Sadrita404/Blinky/Images/1.png

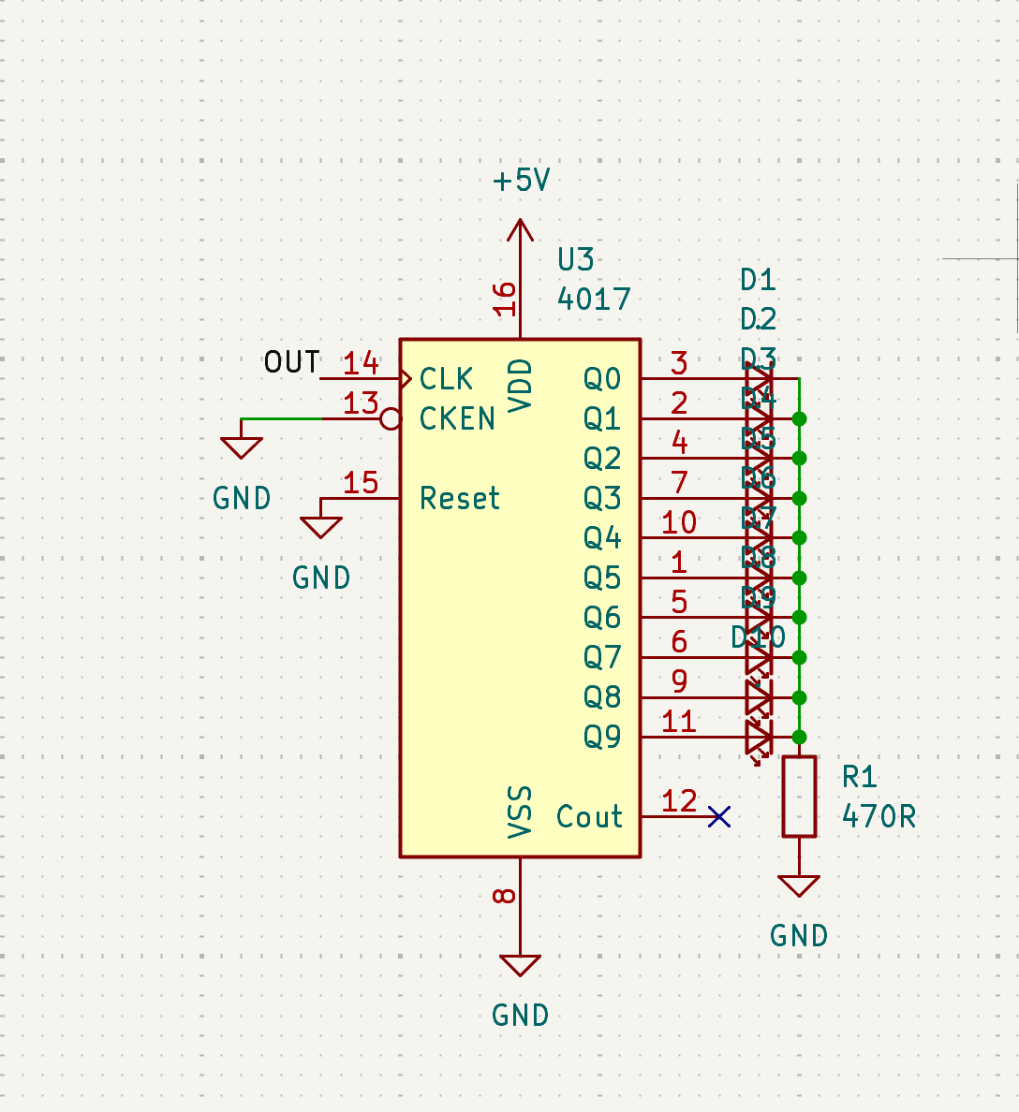
Images/1.png
