Sadrita404/Blinky/Images/2.png

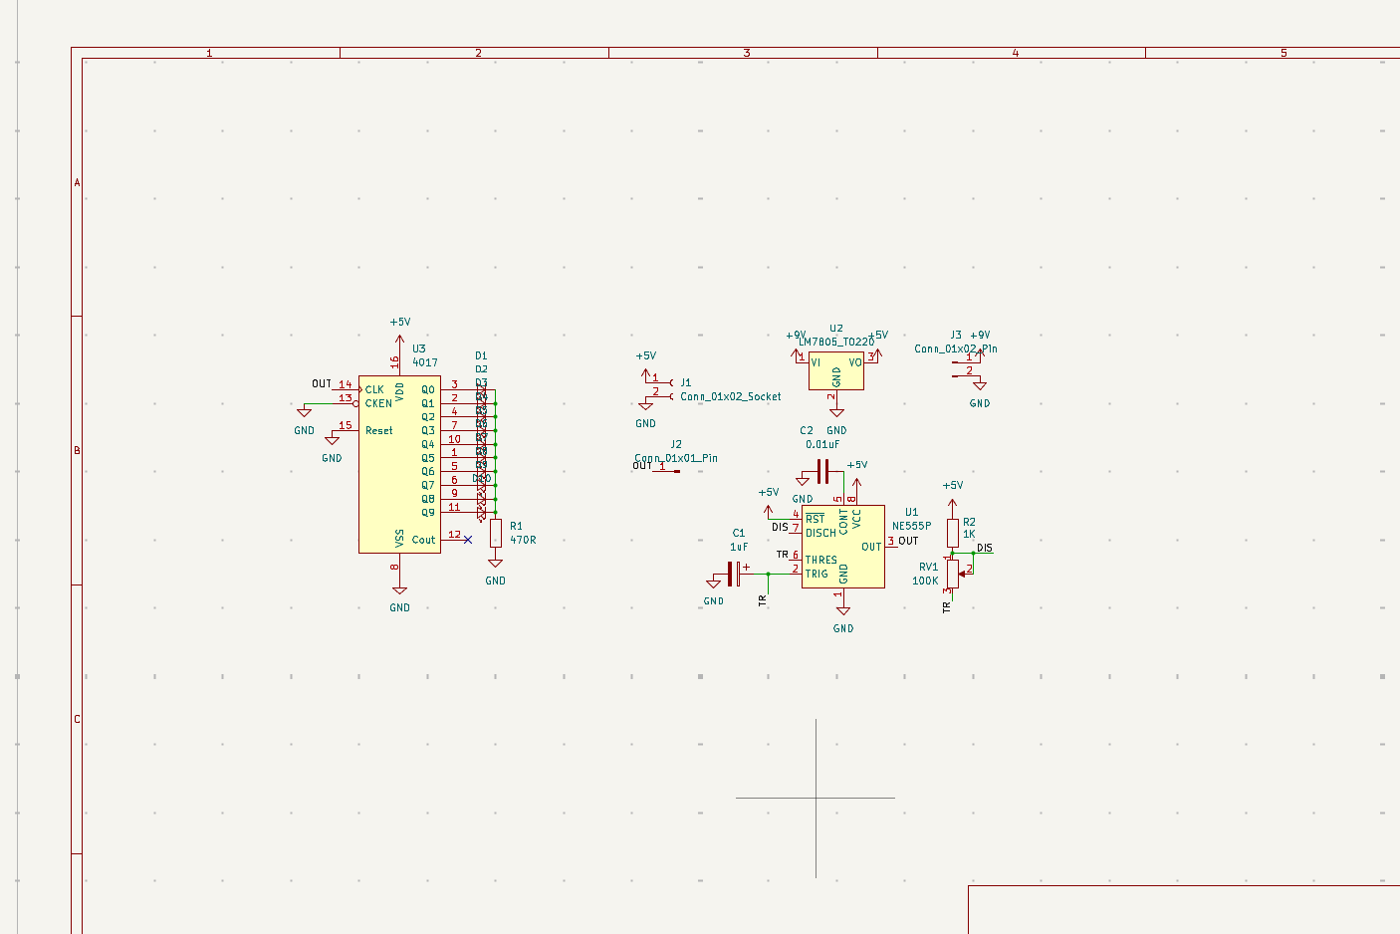
Images/2.png
