Sadrita404/Blinky/Images/3.png

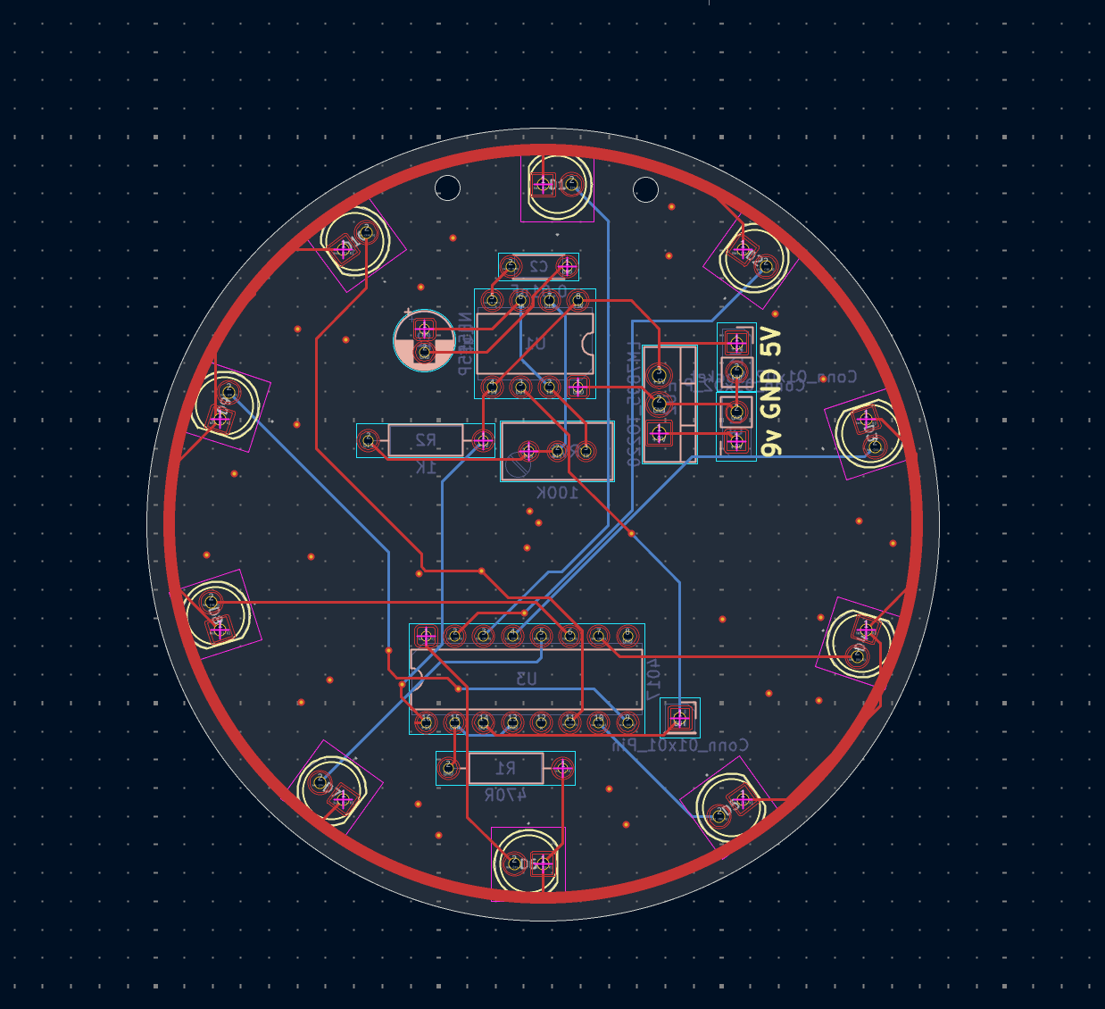
Images/3.png
