Sadrita404/Blinky/Images/4.png

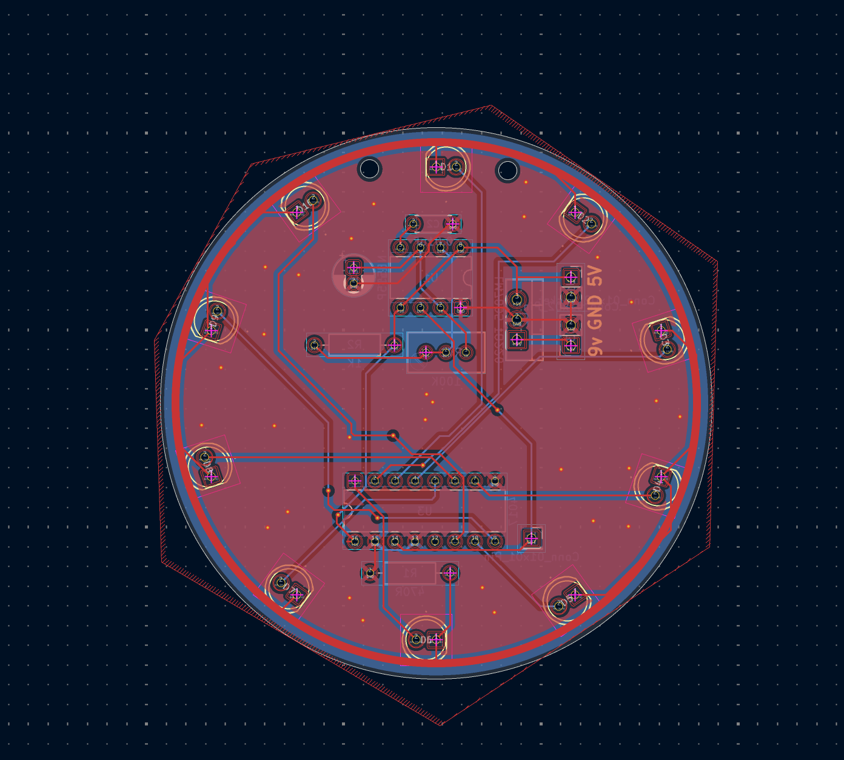
Images/4.png
