Sadrita404/Blinky/Images/5.png

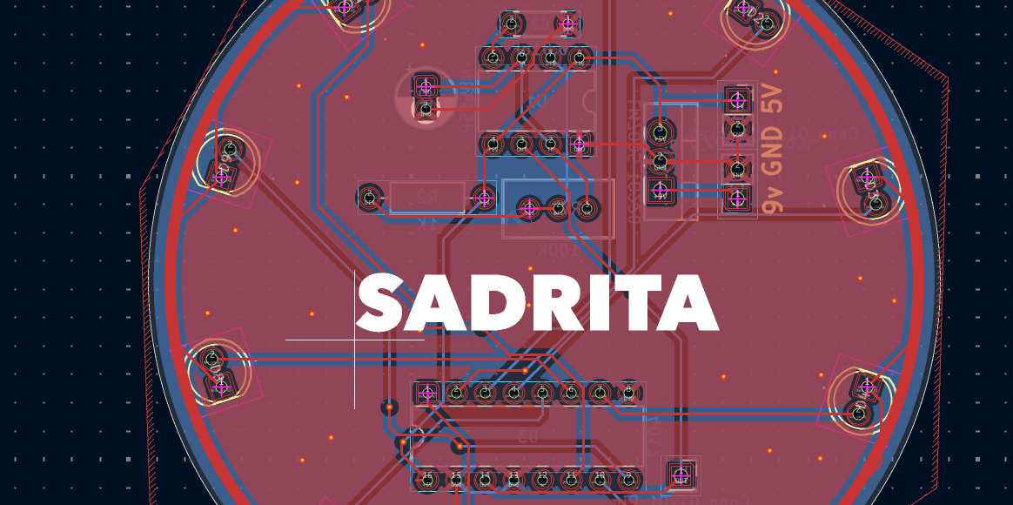
Images/5.png
