Sadrita404/Blinky/Images/6.png

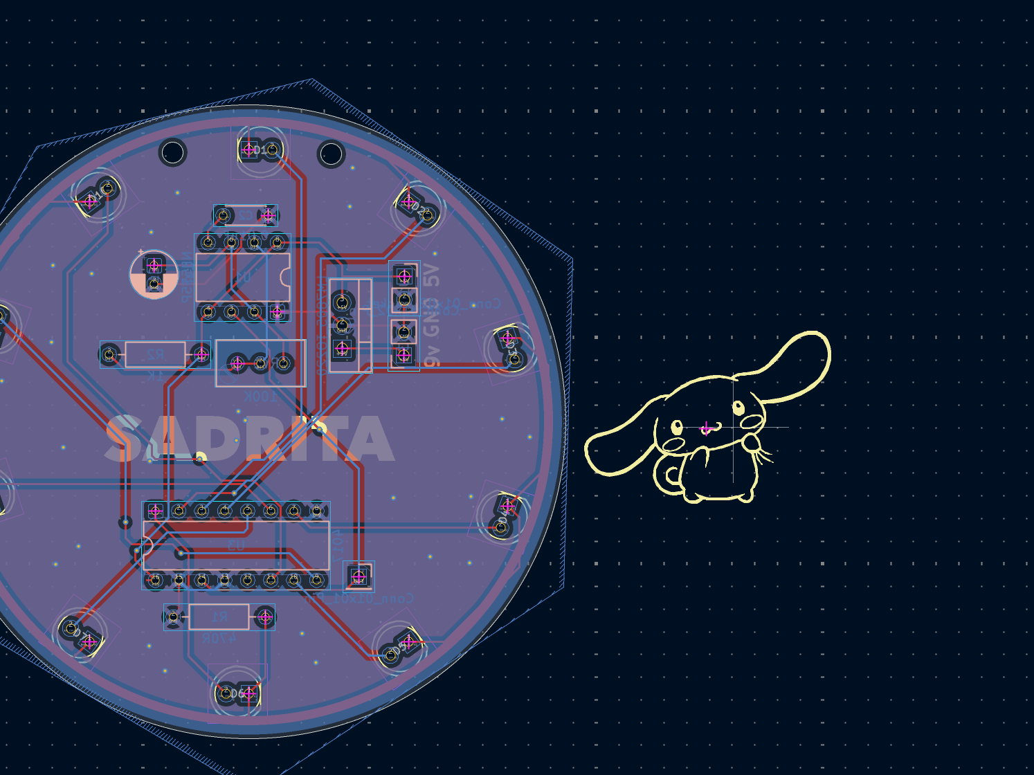
Images/6.png
