Sadrita404/Blinky/Images/7.png

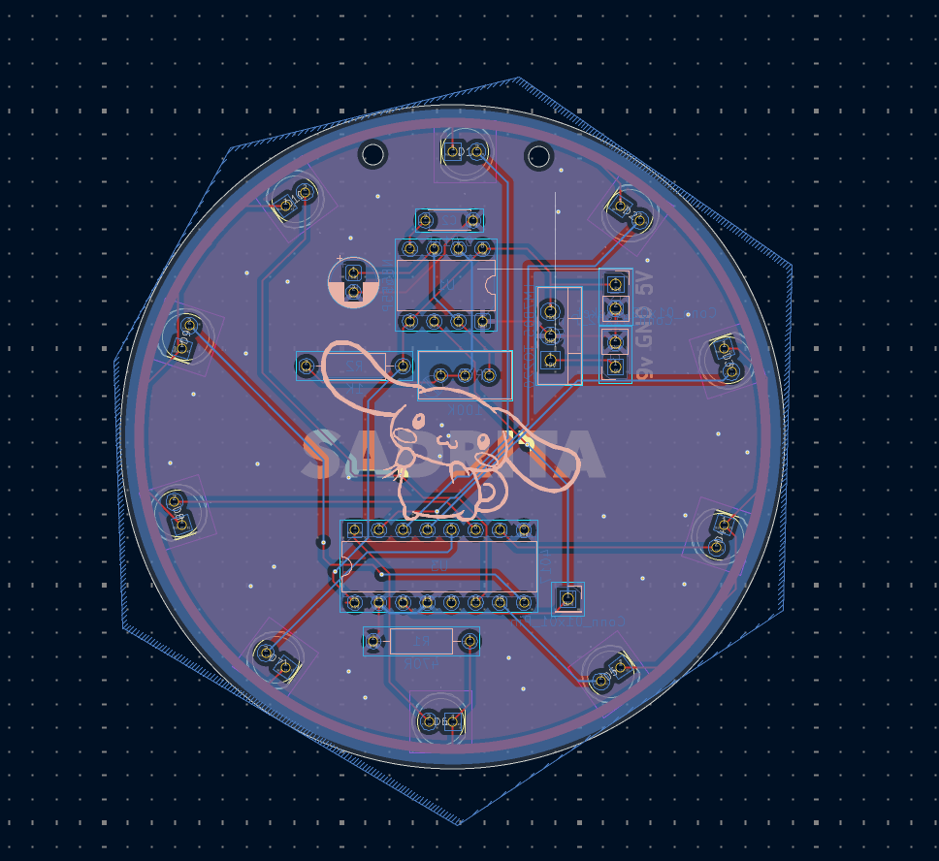
Images/7.png
