Sadrita404/Blinky/Images/8.png

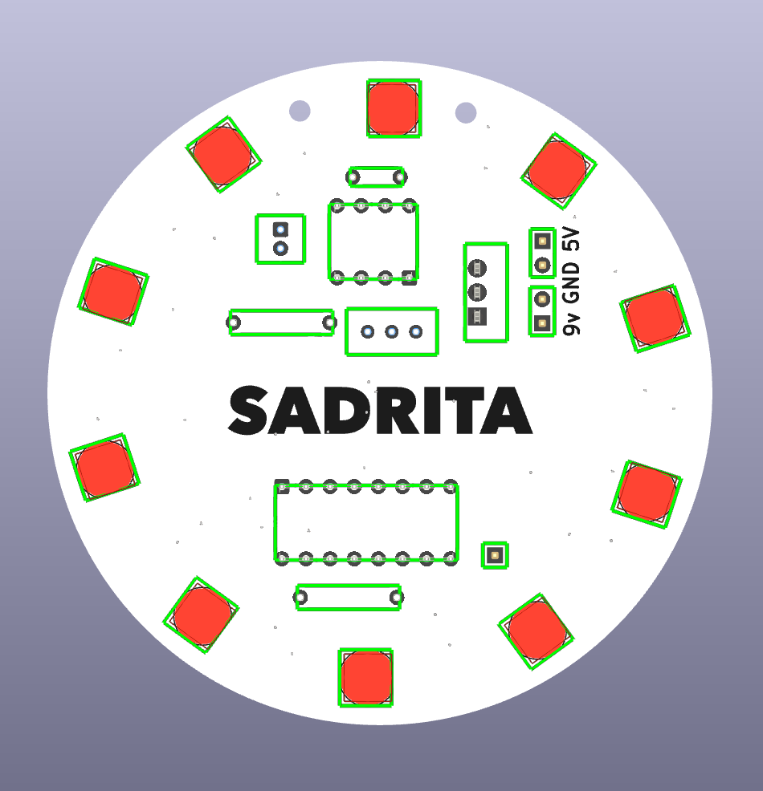
Images/8.png
