Sadrita404/Blinky/Images/9.png

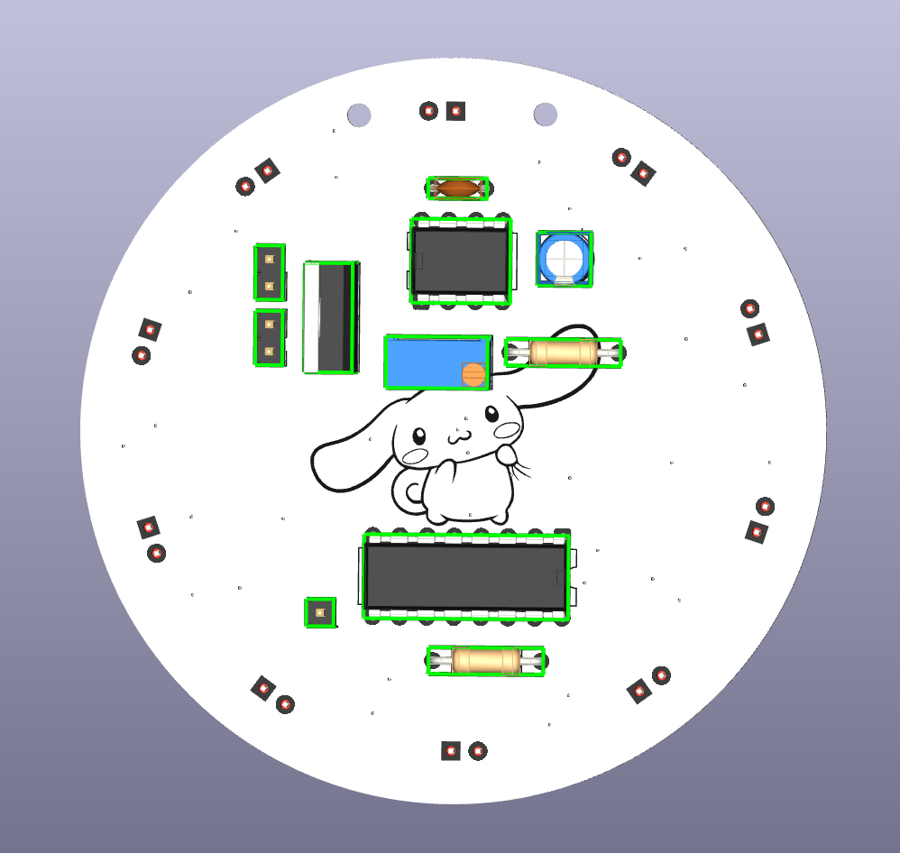
Images/9.png
